jedimatt42/TI-99-usb-keys/TI99USBKeys/USBCodes.h

#ifndef _USB_CODES_H
#define _USB_CODES_H


#define U_BACKQUOTE 0x35
#define U_OPENSQUARE 0x2F
#define U_CLOSESQUARE 0x30
#define U_BACKSLASH 0x31
#define U_SLASH 0x38
#define U_HYPHEN 0x2D
#define U_QUOTE 0x34
#define U_BACKQUOTE 0x35
#define U_EQUAL 0x2E
#define U_SEMICOLON 0x33
#define U_ENTER 0x28
#define U_COMMA 0x36
#define U_PERIOD 0x37
#define U_SPACE 0x2C
#define U_BACKSPACE 0x2A
#define U_LEFTARROW 0x50
#define U_RIGHTARROW 0x4F
#define U_UPARROW 0x52
#define U_DOWNARROW 0x51
#define U_QUOTE 0x34
#define U_HOME 0x4A
#define U_END 0x4D

#define U_F1 0x3A
#define U_F2 0x3B
#define U_F3 0x3C
#define U_F4 0x3D
#define U_F5 0x3E
#define U_F6 0x3F
#define U_F7 0x40
#define U_F8 0x41
#define U_F9 0x42
#define U_F10 0x43
#define U_F11 0x44
#define U_F12 0x45

#define U_DELETE 0x4C
#define U_INSERT 0x49
#define U_BREAK 0x48
#define U_PGDN 0x4E
#define U_PGUP 0x4B
#define U_TAB 0x2B
#define U_ESC 0x29

#define U_CAPSLOCK 0x39

#define U_LEFTSHIFT 32
#define U_RIGHTSHIFT 2
#define U_LEFTALT 64
#define U_RIGHTALT 4
#define U_LEFTCTRL 16
#define U_RIGHTCTRL 1

#define U_NUM1 0x1E
#define U_NUM2 0x1F
#define U_NUM3 0x20
#define U_NUM4 0x21
#define U_NUM5 0x22
#define U_NUM6 0x23
#define U_NUM7 0x24
#define U_NUM8 0x25
#define U_NUM9 0x26
#define U_NUM0 0x27

#define U_NUMPAD_1 0x59
#define U_NUMPAD_2 0x5A
#define U_NUMPAD_3 0x5B
#define U_NUMPAD_4 0x5C
#define U_NUMPAD_5 0x5D
#define U_NUMPAD_6 0x5E
#define U_NUMPAD_7 0x5F
#define U_NUMPAD_8 0x60
#define U_NUMPAD_9 0x61
#define U_NUMPAD_0 0x62
#define U_NUMPAD_PERIOD 0x63
#define U_NUMPAD_SLASH 0x31
#define U_NUMSLASH 0x54
#define U_NUMPAD_STAR 0x55
#define U_NUMPAD_HYPHEN 0x56
#define U_NUMPAD_PLUS 0x57
#define U_NUMPAD_ENTER 0x58

#define U_Q 0x14
#define U_W 0x1A
#define U_E 0x08
#define U_R 0x15
#define U_T 0x17
#define U_Y 0x1C
#define U_U 0x18
#define U_I 0x0C
#define U_O 0x12
#define U_P 0x13

#define U_A 0x04
#define U_S 0x16
#define U_D 0x07
#define U_F 0x09
#define U_G 0x0A
#define U_H 0x0B
#define U_J 0x0D
#define U_K 0x0E
#define U_L 0x0F

#define U_Z 0x1D
#define U_X 0x1B
#define U_C 0x06
#define U_V 0x19
#define U_B 0x05
#define U_N 0x11
#define U_M 0x10

#endif
